telzo2000/tacash36/img/img00014.jpg

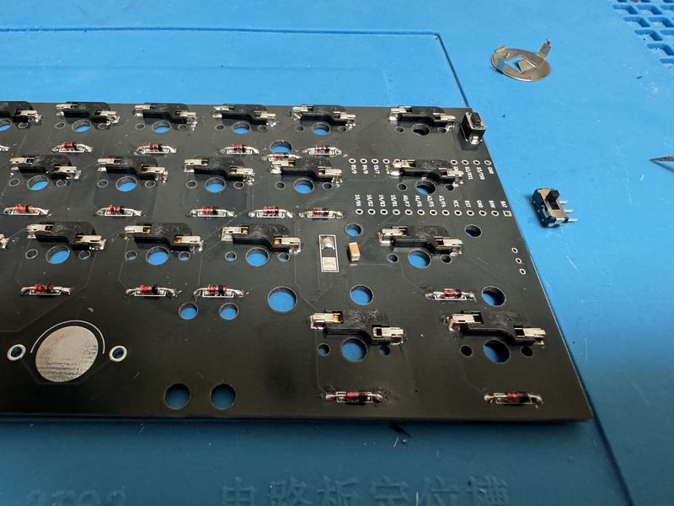
img/img00014.jpg
