telzo2000/tacash36/img/img00017.jpg

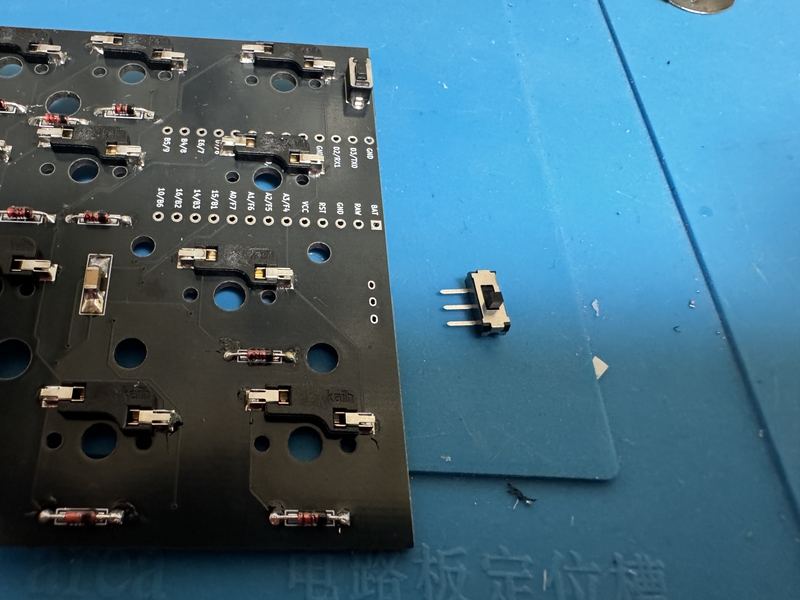
img/img00017.jpg
