telzo2000/tacash36/img/img00034.jpg

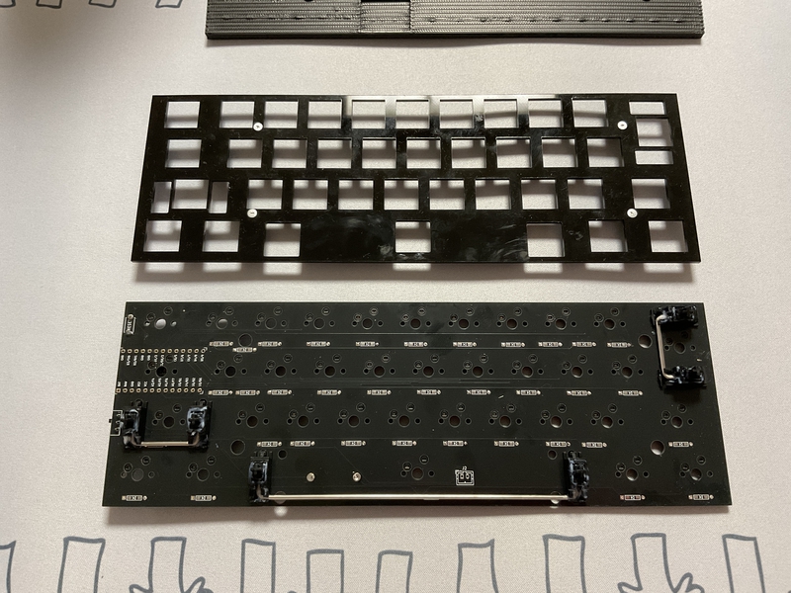
img/img00034.jpg
